cruzb/MIDI-pedal-mesh/midi_mesh/pcb/Mesh.sch

## EAGLE design midi_mesh/pcb/Mesh.sch (2019-12-07)

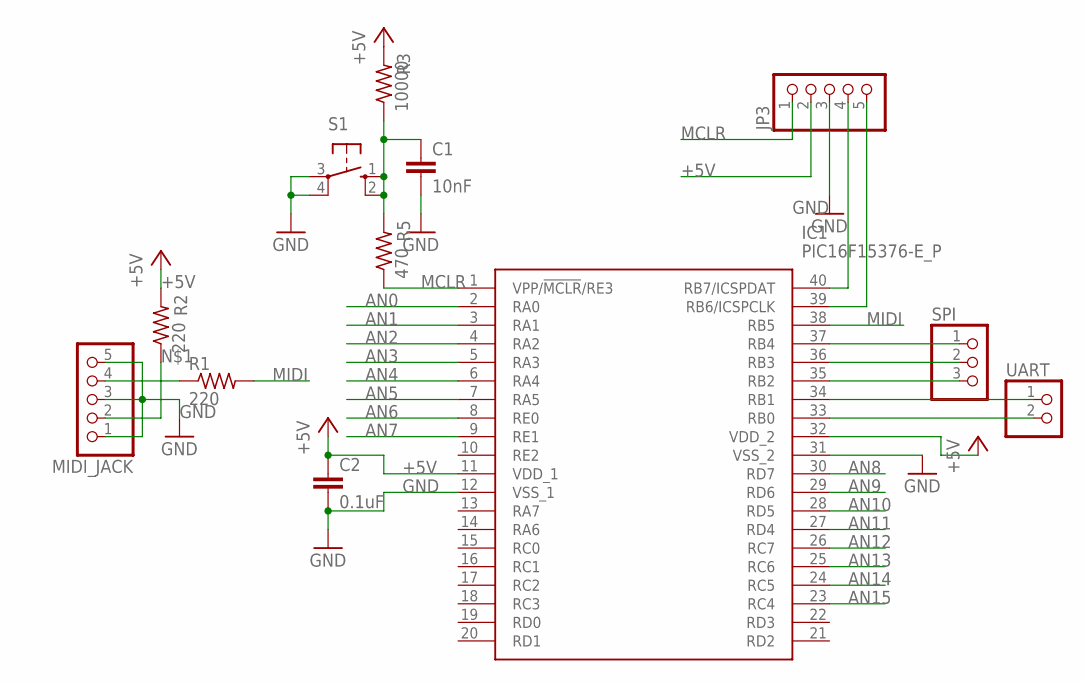
[picture p3: schematic Mesh.sch, sheet 1]

Parts:
C1: 10nF; C0603
C2: 0.1uF; C0603
IC1: PIC16F15376-E_P; DIP1543W58P254L5175H635Q40N
JP3: PINHD-1X5; 1X05
MIDI_JACK: PINHD-1X5; 1X05
R1, R2: 220; R0603
R3: 10000; R0603
R5: 470; R0603
S1: 10-XX; B3F-10XX
SPI: PINHD-1X3; 1X03
UART: PINHD-1X2; 1X02

Connections:
+5V: C2.1, IC1.11 (VDD_1), IC1.32 (VDD_2), JP3.2, R2.2, R3.2
AN0: IC1.2 (RA0)
AN1: IC1.3 (RA1)
AN2: IC1.4 (RA2)
AN3: IC1.5 (RA3)
AN4: IC1.6 (RA4)
AN5: IC1.7 (RA5)
AN6: IC1.8 (RE0)
AN7: IC1.9 (RE1)
AN8: IC1.30 (RD7)
AN9: IC1.29 (RD6)
AN10: IC1.28 (RD5)
AN11: IC1.27 (RD4)
AN12: IC1.26 (RC7)
AN13: IC1.25 (RC6)
AN14: IC1.24 (RC5)
AN15: IC1.23 (RC4)
GND: C1.2, C2.2, IC1.12 (VSS_1), IC1.31 (VSS_2), JP3.3, MIDI_JACK.1, MIDI_JACK.3, MIDI_JACK.5, S1.3, S1.4 (P1)
MCLR: C1.1, IC1.1 (VPP/!MCLR!/RE3), JP3.1, R3.1, R5.1, R5.2, S1.1 (S), S1.2 (S1)
MIDI: IC1.38 (RB5), R1.2
unnamed: MIDI_JACK.2, R2.1
unnamed: IC1.33 (RB0), UART.2
unnamed: IC1.34 (RB1), UART.1
unnamed: IC1.35 (RB2), SPI.3
unnamed: MIDI_JACK.4, R1.1
unnamed: IC1.36 (RB3), SPI.2
unnamed: IC1.37 (RB4), SPI.1
unnamed: IC1.40 (RB7/ICSPDAT), JP3.4
unnamed: IC1.39 (RB6/ICSPCLK), JP3.5

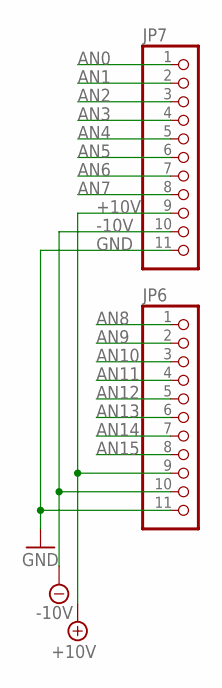
[picture p4: schematic Mesh.sch, sheet 2]

Parts:
JP6, JP7: PINHD-1X11/90; 1X11/90

Connections:
+10V: JP6.9, JP7.9
-10V: JP6.10, JP7.10
AN0: JP7.1
AN1: JP7.2
AN2: JP7.3
AN3: JP7.4
AN4: JP7.5
AN5: JP7.6
AN6: JP7.7
AN7: JP7.8
AN8: JP6.1
AN9: JP6.2
AN10: JP6.3
AN11: JP6.4
AN12: JP6.5
AN13: JP6.6
AN14: JP6.7
AN15: JP6.8
GND: JP6.11, JP7.11

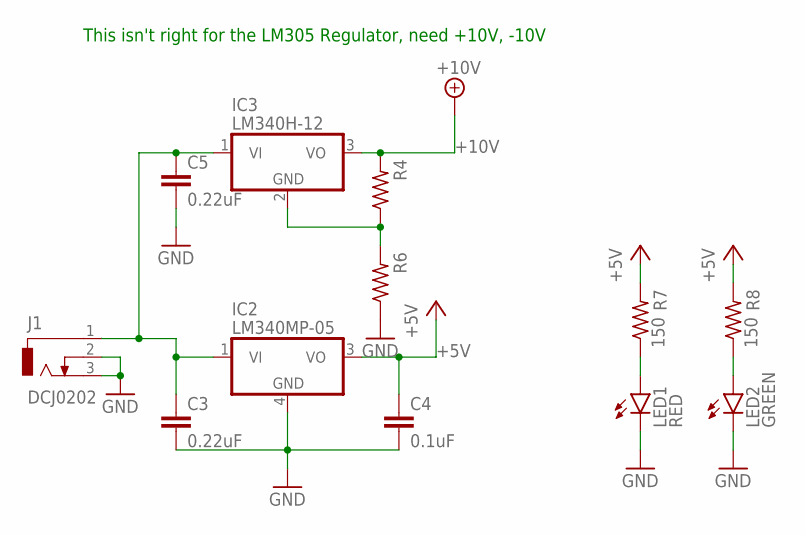
[picture p5: schematic Mesh.sch, sheet 3]

Parts:
C3, C5: 0.22uF; C0603
C4: 0.1uF; C0603
IC2: LM340MP-05; SOT223
IC3: LM340H-12; TO220H
J1: DCJ0202
LED1: RED; CHIP-LED0603
LED2: GREEN; CHIP-LED0603
R4, R6: R-US_R0603; R0603
R7, R8: 150; R0603

Connections:
+5V: C4.1, IC2.3 (VO), R7.2, R8.2
+10V: IC3.3 (VO), R4.2
GND: C3.2, C4.2, C5.2, IC2.4 (GND), J1.2, J1.3, LED1.C, LED2.C, R6.1
unnamed: IC3.2 (GND), R4.1, R6.2
unnamed: C3.1, C5.1, IC2.1 (VI), IC3.1 (VI), J1.1
unnamed: LED1.A, R7.1
unnamed: LED2.A, R8.1

Notes on the sheet:
This isn't right for the LM305 Regulator, need +10V, -10V

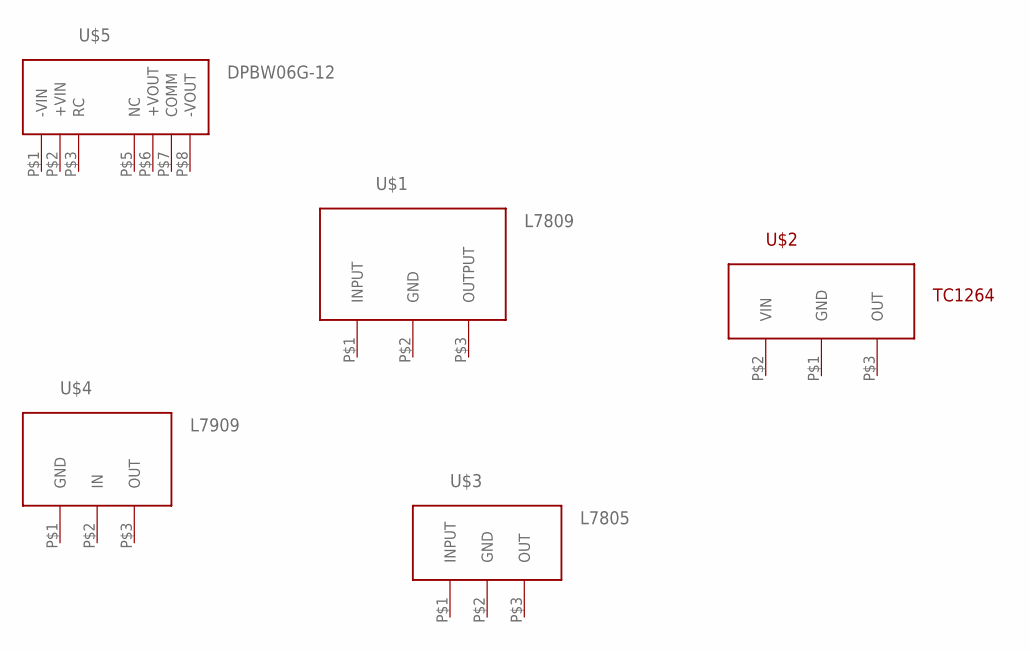
[picture p6: schematic Mesh.sch, sheet 4]

Parts:
U$1: L7809
U$2: TC1264
U$3: L7805
U$4: L7909
U$5: DPBW06G-12
